jkorinth/fear_the_creeper/hw/creeper/components/LIS2DH12TR/LGA-12_STM.step

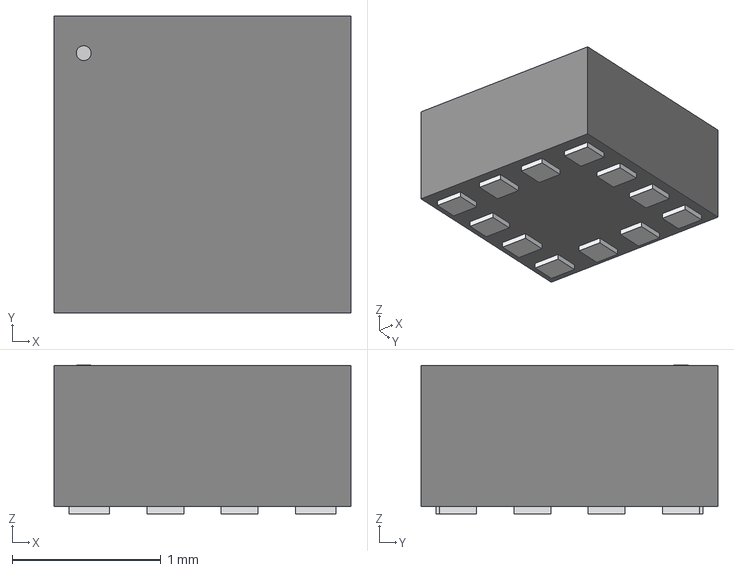
[picture p17: CAD file, 2025-08-20]
hw/creeper/components/LIS2DH12TR/LGA-12_STM.step
2.00 x 2.00 x 1.00 mm
