jkorinth/fear_the_creeper/hw/creeper/components/LP_T67F/LED_LPT67F-P1R2-35-1-20-R18_AMS.step

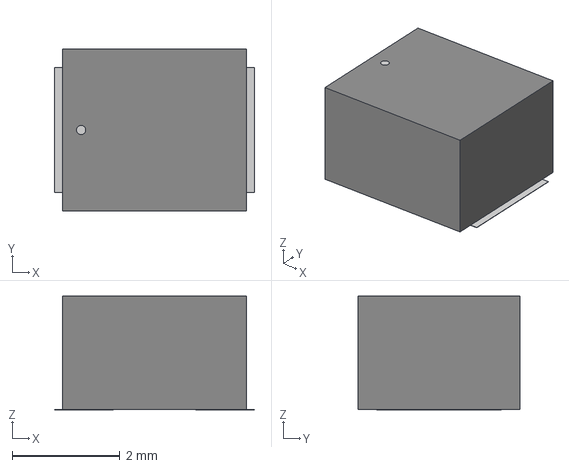
[picture p18: CAD file, 2025-08-20]
hw/creeper/components/LP_T67F/LED_LPT67F-P1R2-35-1-20-R18_AMS.step
3.71 x 3.00 x 2.11 mm
