jkorinth/fear_the_creeper/hw/creeper/components/PT_1241PFQ/PT-1241PFQ_MAL.step

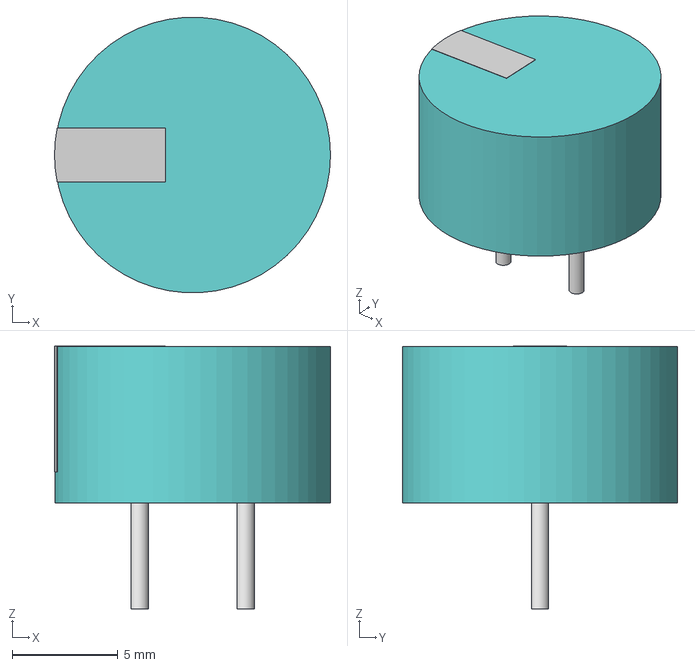
[picture p19: CAD file, 2025-10-01]
hw/creeper/components/PT_1241PFQ/PT-1241PFQ_MAL.step
13.0 x 13.0 x 12.4 mm
