jkorinth/fear_the_creeper/hw/creeper/components/SMT-0825-S-2-R/SMT-0825-S-2-R.step

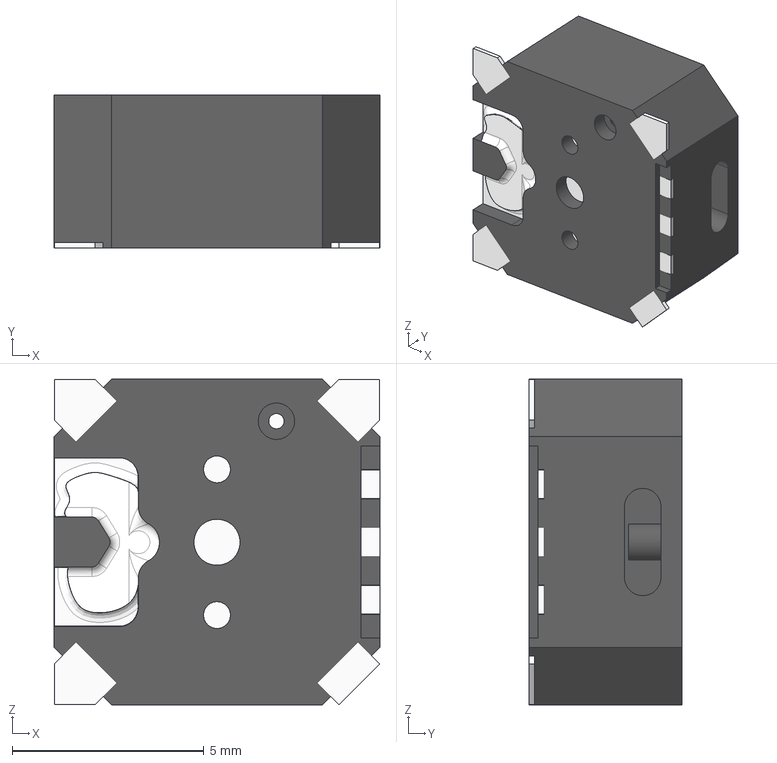
[picture p20: CAD file, 2025-10-01]
hw/creeper/components/SMT-0825-S-2-R/SMT-0825-S-2-R.step
8.50 x 4.00 x 8.50 mm
