jkorinth/fear_the_creeper/hw/creeper/components/SMT_1324_TW_1V_HT_R/SMT-1324-TW-1V-HT-R.step

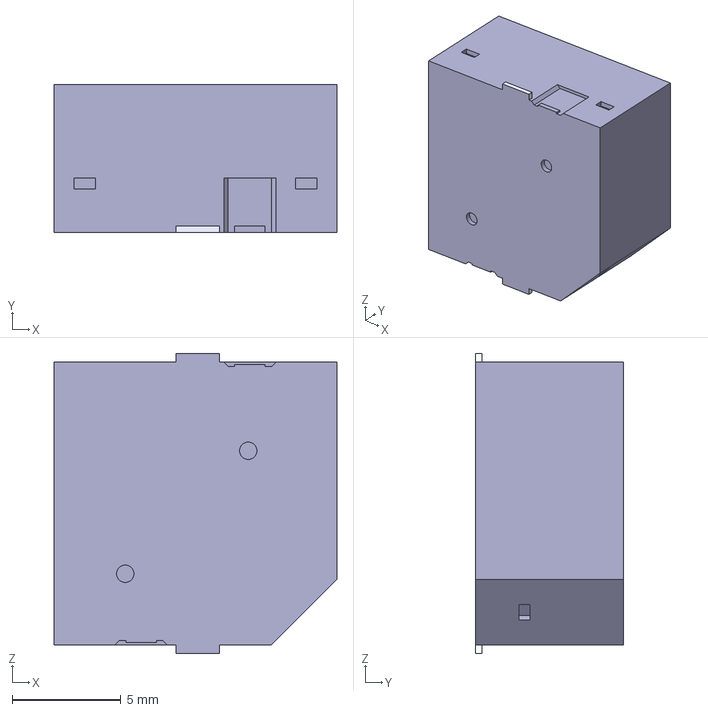
[picture p21: CAD file, 2025-08-20]
hw/creeper/components/SMT_1324_TW_1V_HT_R/SMT-1324-TW-1V-HT-R.step
13.0 x 6.80 x 13.8 mm
