jkorinth/fear_the_creeper/case/v3/creeper_case_v3_face.stl

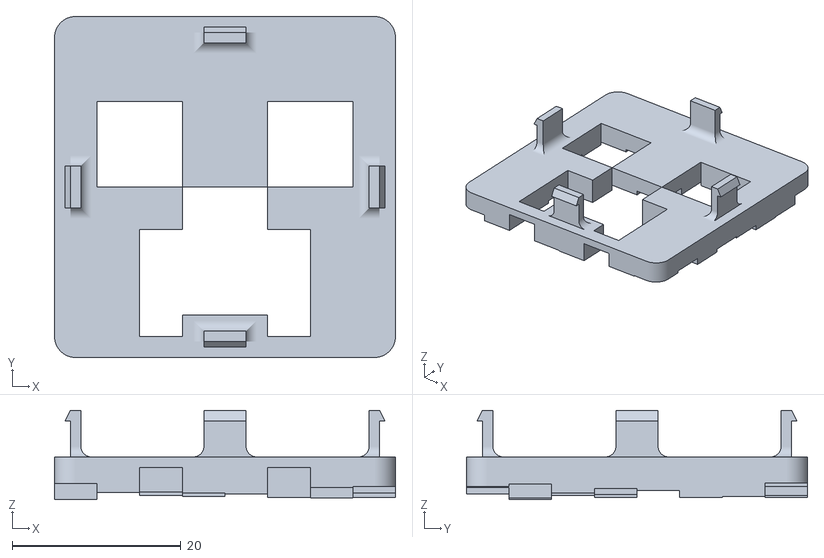
[picture p23: CAD file, 2025-08-20]
case/v3/creeper_case_v3_face.stl
40.4 x 40.4 x 10.5
