jkorinth/fear_the_creeper/sw/include/lut.h

#pragma once
#include <avr/pgmspace.h>
static const long LUT[] PROGMEM = {
 1000010,  904847,  818740,  740828,  670330,  606540,  548821,  496595,
  449338,  406579,  367889,  332881,  301204,  272541,  246606,  223140,
  201906,  182693,  165308,  149578,  135345,  122466,  110813,  100268,
   90727,   82094,   74283,   67215,   60820,   55033,   49797,   45059,
   40772,   36893,   33383,   30207,   27333,   24733,   22380,   20251,
   18325,   16582,   15005,   13578,   12287,   11118,   10061,    9105,
    8239,    7456,    6747,    6106,    5526,    5001,    4526,    4096,
    3707,    3355,    3037,    2749,    2488,    2252,    2039,    1846,
    1671,    1513,    1370,    1240,    1123,    1017,     921,     835,
     756,     685,     621,     563,     510,     462,     419,     380,
     345,     313,     284,     258,     234,     213,     194,     176,
     160,     146,     133,     121,     111,     101,      92,      84,
      77,      71,      65,      60
};
